femtofox/Femtofox_Community_Hardware/Pictures/06 ignore warning.webp

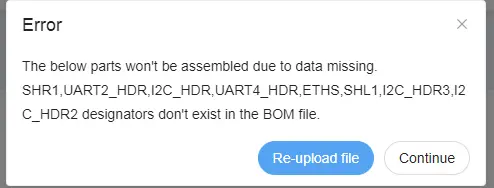
Pictures/06 ignore warning.webp
